Aberdeen-Skunkworks/Nanofluids/VXI_Scripts/PythonController/CalibrationResults/04-03-20-19.csv

# | SW | SW (t) | LW | LW (t) | TP (ohm) | Temp Probe (*C) | TP (t) | PT_6 (ohm) | PT_6 (*C) | PT_6 (t) | PT_1 (ohm) | PT_1 (*C) | PT_1 (t) | PT_2 (ohm) | PT_2 (*C) | PT_2 (t) | PT_3 (ohm) | PT_3 (*C) | PT_3 (t) | PT_4 (ohm) | PT_4 (*C) | PT_4 (t) | PT_5 (ohm) | PT_5 (*C) | PT_5 (t)
0 | 39.19531 | 20:19:31.886553 | 57.46484 | 20:19:31.959413 | 110.2324 | 26.28386950776904 | 20:19:32.025238 | 1212.633 | 27.54528905943455 | 20:19:32.101097 | 1212.078 | 27.43365820432441 | 20:19:32.168863 | 1203.264 | 25.65680686458673 | 20:19:32.243704 | 1203.965 | 25.79840317244107 | 20:19:32.309964 | 1268.045 | -309.8126919326622 | 20:19:32.386268 | 1213.24 | 27.667344724196482 | 20:19:32.452092
1 | 39.19141 | 20:19:32.546838 | 57.46289 | 20:19:32.611943 | 110.2305 | 26.27897033784451 | 20:19:32.687696 | 1212.643 | 27.54730015138676 | 20:19:32.754533 | 1212.088 | 27.43566983622501 | 20:19:32.832343 | 1203.266 | 25.65721091713242 | 20:19:32.906180 | 1203.977 | 25.800826654149528 | 20:19:32.971925 | 1268.053 | -309.81205293691545 | 20:19:33.038746 | 1213.248 | 27.668953126457698 | 20:19:33.112560
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
