Aberdeen-Skunkworks/Nanofluids/VXI_Scripts/PythonController/CalibrationResults/04-05-20-02.csv

# | SW | SW (t) | LW | LW (t) | TP (ohm) | Temp Probe (*C) | TP (t) | PT_6 (ohm) | PT_6 (*C) | PT_6 (t) | PT_1 (ohm) | PT_1 (*C) | PT_1 (t) | PT_2 (ohm) | PT_2 (*C) | PT_2 (t) | PT_3 (ohm) | PT_3 (*C) | PT_3 (t) | PT_4 (ohm) | PT_4 (*C) | PT_4 (t) | PT_5 (ohm) | PT_5 (*C) | PT_5 (t)
0 | 38.47949 | 20:02:01.558758 | 56.38086 | 20:02:02.373777 | 107.9351 | 20.365328184320195 | 20:02:03.190399 | 1184.348 | 21.81751998311626 | 20:02:04.011229 | 1185.405 | 22.03299808149471 | 20:02:04.842910 | 1175.857 | 20.08245690746049 | 20:02:05.658534 | 1176.881 | 20.292090976482157 | 20:02:06.475752 | 1239.215 | -312.13087202282463 | 20:02:07.292367 | 1185.58 | 22.068662397809742 | 20:02:08.108959
1 | 38.47803 | 20:02:08.944734 | 56.37891 | 20:02:09.775989 | 107.9468 | 20.395445252847672 | 20:02:10.593092 | 1184.345 | 21.816908248221928 | 20:02:11.423937 | 1185.401 | 22.032182861054423 | 20:02:12.243076 | 1175.85 | 20.08102349405216 | 20:02:13.059184 | 1176.874 | 20.29065829394177 | 20:02:13.875083 | 1239.209 | -312.13135771930433 | 20:02:14.692226 | 1185.575 | 22.067643460157832 | 20:02:15.524020
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
