Aberdeen-Skunkworks/Nanofluids/VXI_Scripts/PythonController/CalibrationResults/04-05-20-05.csv

# | SW | SW (t) | LW | LW (t) | TP (ohm) | Temp Probe (*C) | TP (t) | PT_6 (ohm) | PT_6 (*C) | PT_6 (t) | PT_1 (ohm) | PT_1 (*C) | PT_1 (t) | PT_2 (ohm) | PT_2 (*C) | PT_2 (t) | PT_3 (ohm) | PT_3 (*C) | PT_3 (t) | PT_4 (ohm) | PT_4 (*C) | PT_4 (t) | PT_5 (ohm) | PT_5 (*C) | PT_5 (t)
0 | 38.47217 | 20:05:54.922730 | 56.37158 | 20:05:55.738559 | 108.1328 | 20.874264691964726 | 20:05:56.554453 | 1184.18 | 21.783261430529535 | 20:05:57.372551 | 1185.225 | 21.996311565599022 | 20:05:58.192774 | 1175.662 | 20.042524234973293 | 20:05:59.024227 | 1176.685 | 20.251973977919313 | 20:05:59.841571 | 1239.0 | -312.14827700011284 | 20:06:00.657553 | 1185.375 | 22.026883888897327 | 20:06:01.472391
1 | 38.47314 | 20:06:02.325675 | 56.37256 | 20:06:03.142487 | 108.1362 | 20.883017923120967 | 20:06:03.958916 | 1184.176 | 21.782445715993177 | 20:06:04.776487 | 1185.22 | 21.9952924491067 | 20:06:05.595935 | 1175.654 | 20.04088588862269 | 20:06:06.411394 | 1176.68 | 20.250950533888613 | 20:06:07.228110 | 1238.997 | -312.14851987268327 | 20:06:08.044331 | 1185.37 | 22.0258648479815 | 20:06:08.861029
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
