Aberdeen-Skunkworks/Nanofluids/test.py

import numpy as np
import serial
#import visa
import os

import thw

print(serial.tools.list_ports.comports()[1].device)   

# sim = thw.TransientHeatedWire()

# print("program: ", sim.ser)

# Vmeter.chunk_size = 102400

# print(sim)
